titouan73/macropad/Images/IMG_20240912_13465852.jpg

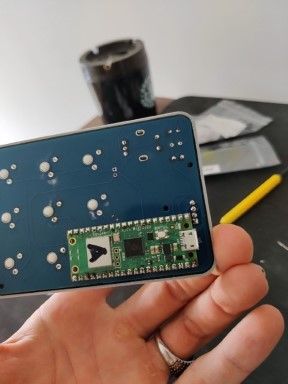
Images/IMG_20240912_13465852.jpg
